circuitvalley/ultrazed_base_boards/Ultrabase_PCIe/Manufacturing/Images/Ultrabase  Open source Ultrazed PCIe Carrier Card for Xilinx AMD Zynq Ultrascale+ FPGA SOC SOM (1).png

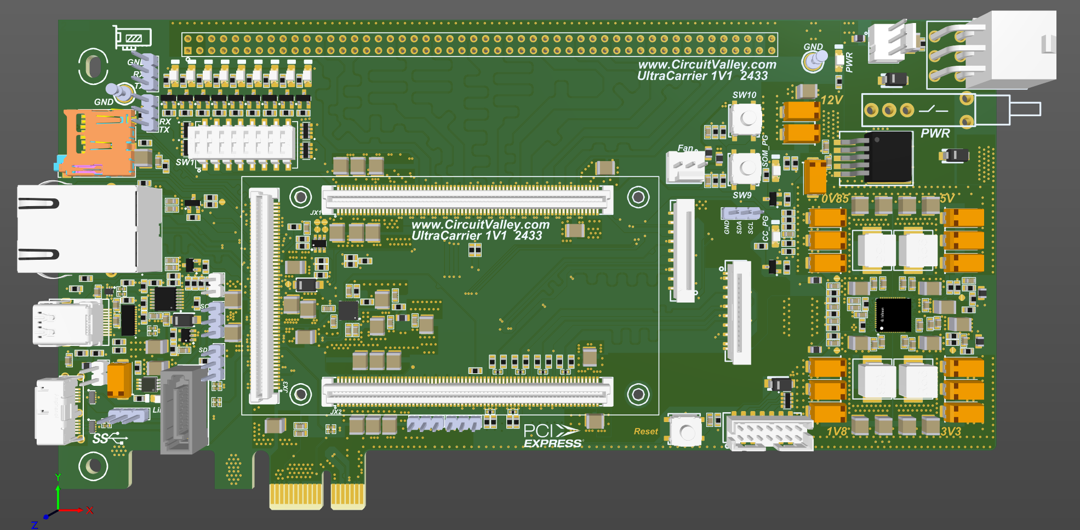
Ultrabase_PCIe/Manufacturing/Images/Ultrabase Open source Ultrazed PCIe Carrier Card for Xilinx AMD Zynq Ultrascale+ FPGA SOC SOM (1).png
