circuitvalley/ultrazed_base_boards/Ultrabase_PCIe/Manufacturing/Images/Ultrabase  Open source Ultrazed PCIe Carrier Card for Xilinx AMD Zynq Ultrascale+ FPGA SOC SOM (7).JPG

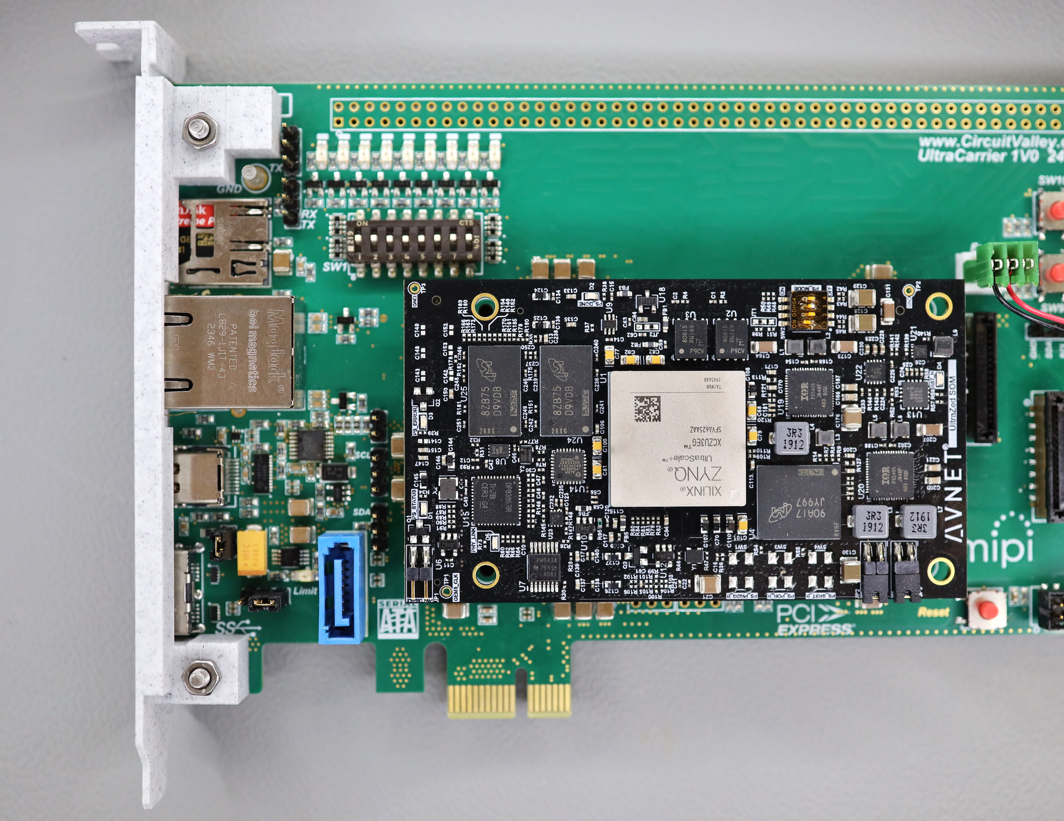
Ultrabase_PCIe/Manufacturing/Images/Ultrabase Open source Ultrazed PCIe Carrier Card for Xilinx AMD Zynq Ultrascale+ FPGA SOC SOM (7).JPG
