circuitvalley/ultrazed_base_boards/Ultrabase_PCIe/Manufacturing/Images/Tests/xilinx_avnet_ultrascale_custom_board (1).png

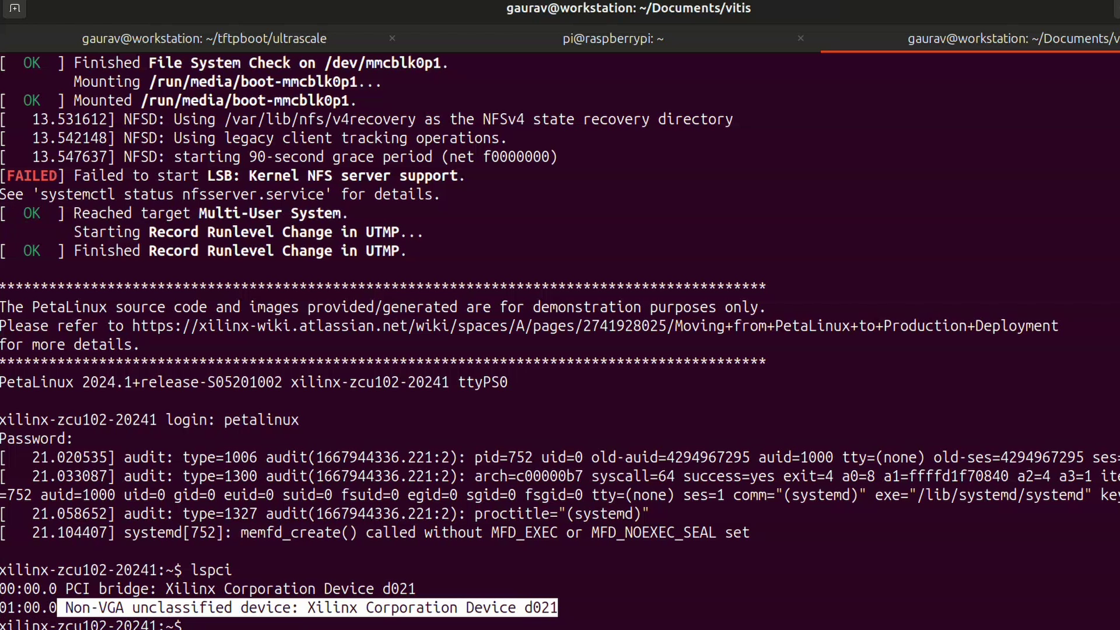
Ultrabase_PCIe/Manufacturing/Images/Tests/xilinx_avnet_ultrascale_custom_board (1).png
