circuitvalley/ultrazed_base_boards/Ultrabase_PCIe/Manufacturing/Images/Tests/xilinx_avnet_ultrascale_custom_board (3).png

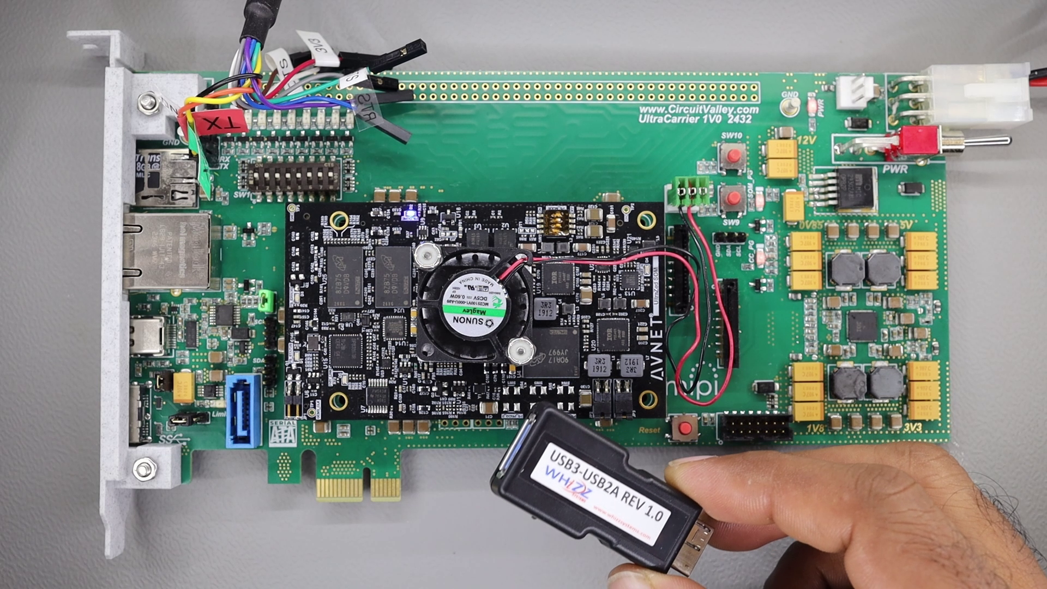
Ultrabase_PCIe/Manufacturing/Images/Tests/xilinx_avnet_ultrascale_custom_board (3).png
